myriadrf/reference-development-kit/myriadrf-1/v1/previous/VIA_OFF_PAD_v.1_r.0/PDF/MYRIAD_RF_PCB Edges.pdf

C:\Import.bin L10: MYRIAD_RF-PCB_Edges.gbr (SIG)
