myriadrf/reference-development-kit/myriadrf-1/v1/previous/VIA_OFF_PAD_v.1_r.0/PDF/MYRIAD_RF_NC Drill.pdf

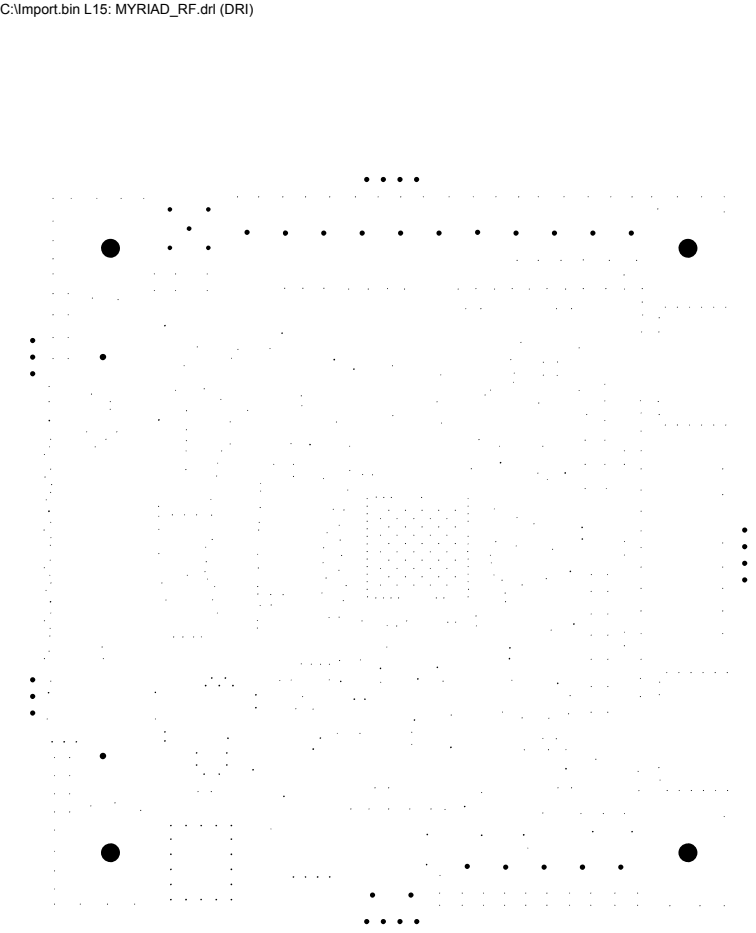
[picture p5: page 1]

C:\Import.bin L15: MYRIAD_RF.drl (DRI)
