myriadrf/reference-development-kit/myriadrf-1/v1/previous/VIA_IN_PAD_v.1_r.0/PDF/MYRIAD_RF_Drill map.pdf

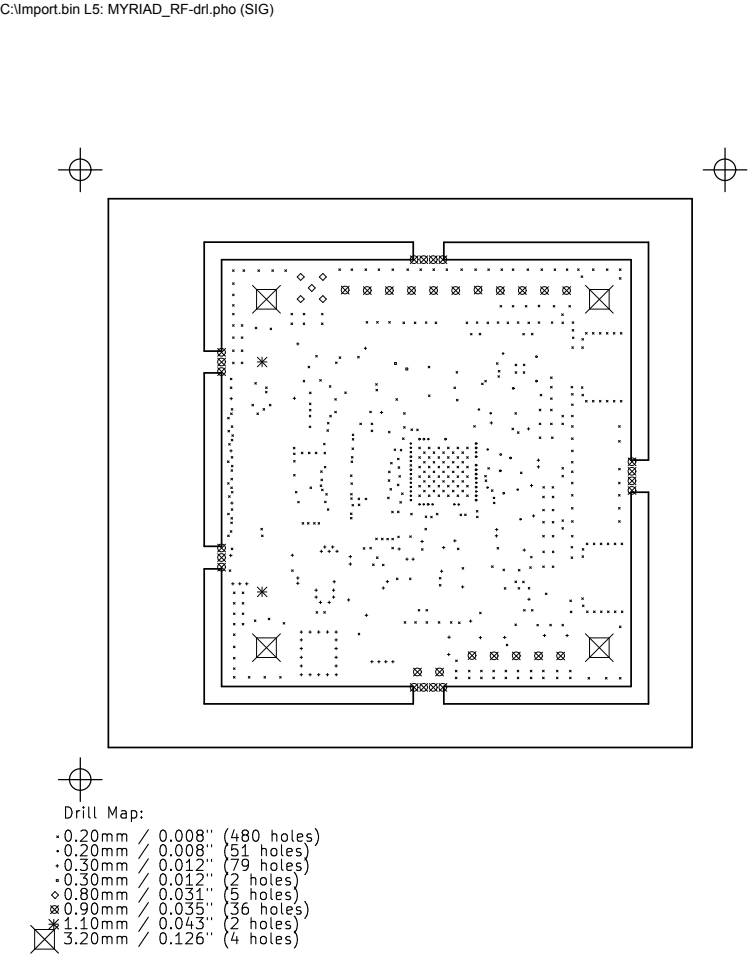
[picture p49: page 1]

C:\Import.bin L5: MYRIAD_RF-drl.pho (SIG)
