myriadrf/reference-development-kit/myriadrf-1/v1/previous/VIA_IN_PAD_v.1_r.0/PDF/MYRIAD_RF_Layouts.pdf

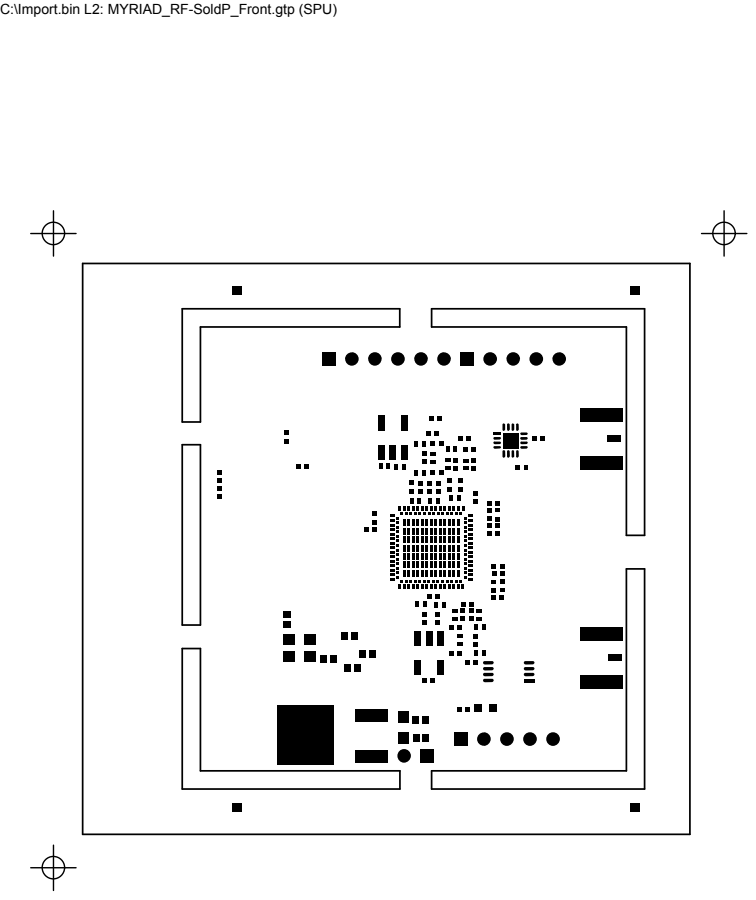
[picture p50: page 1]

C:\Import.bin L2: MYRIAD_RF-SoldP_Front.gtp (SPU)

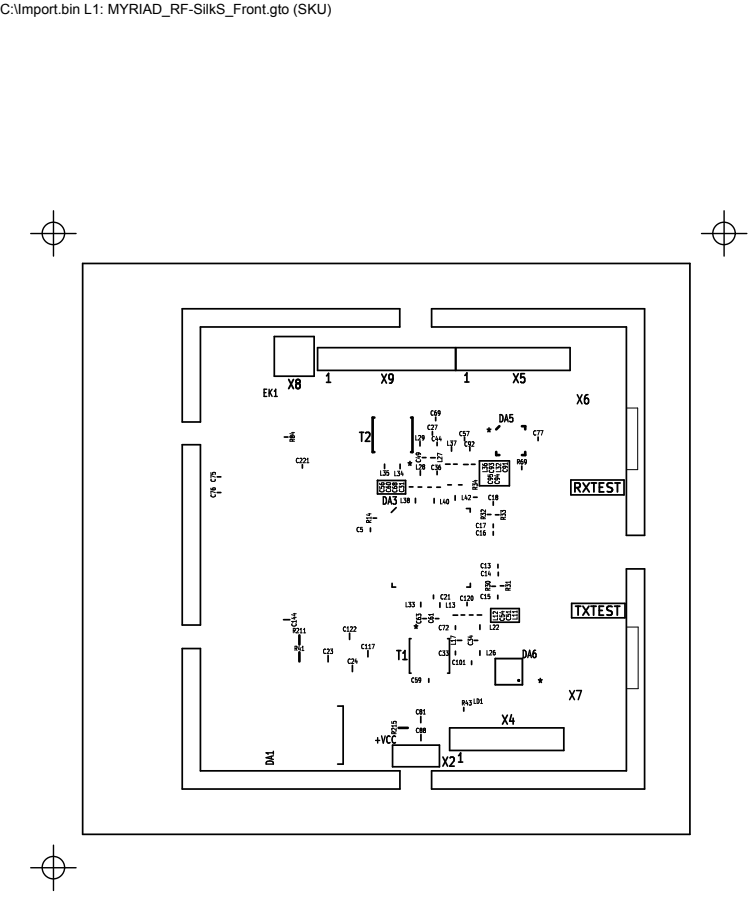
[picture p51: page 2]

C:\Import.bin L1: MYRIAD_RF-SilkS_Front.gto (SKU)

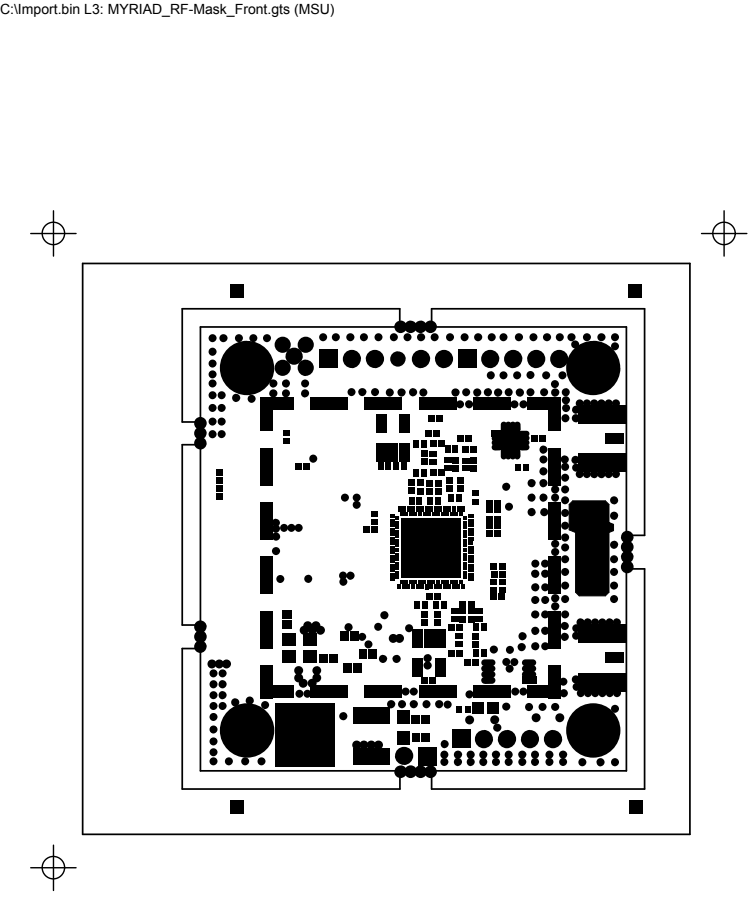
[picture p52: page 3]

C:\Import.bin L3: MYRIAD_RF-Mask_Front.gts (MSU)

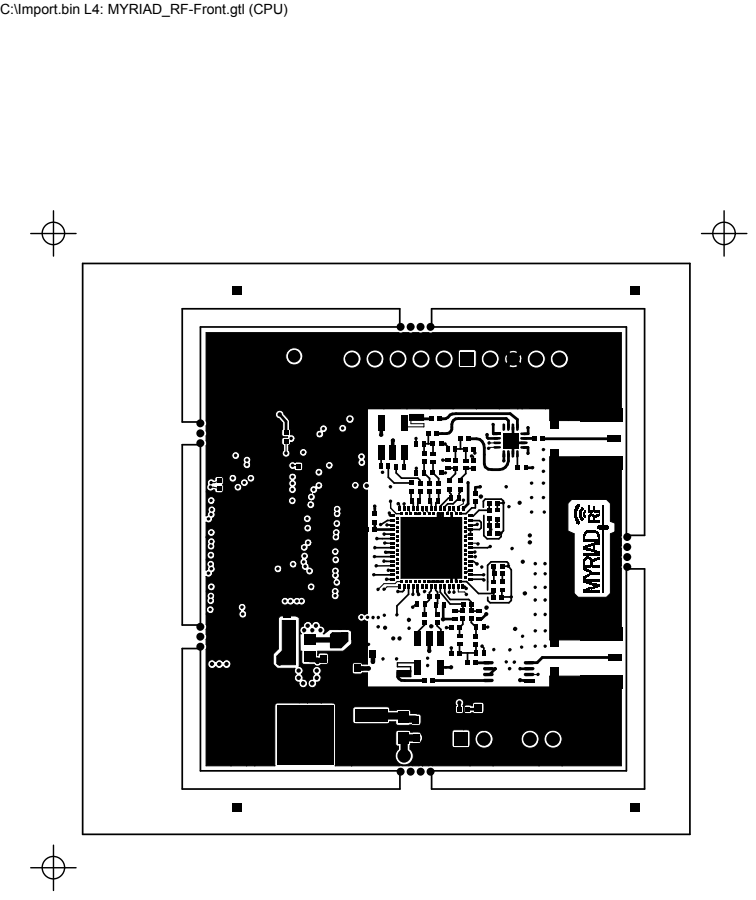
[picture p53: page 4]

C:\Import.bin L4: MYRIAD_RF-Front.gtl (CPU)

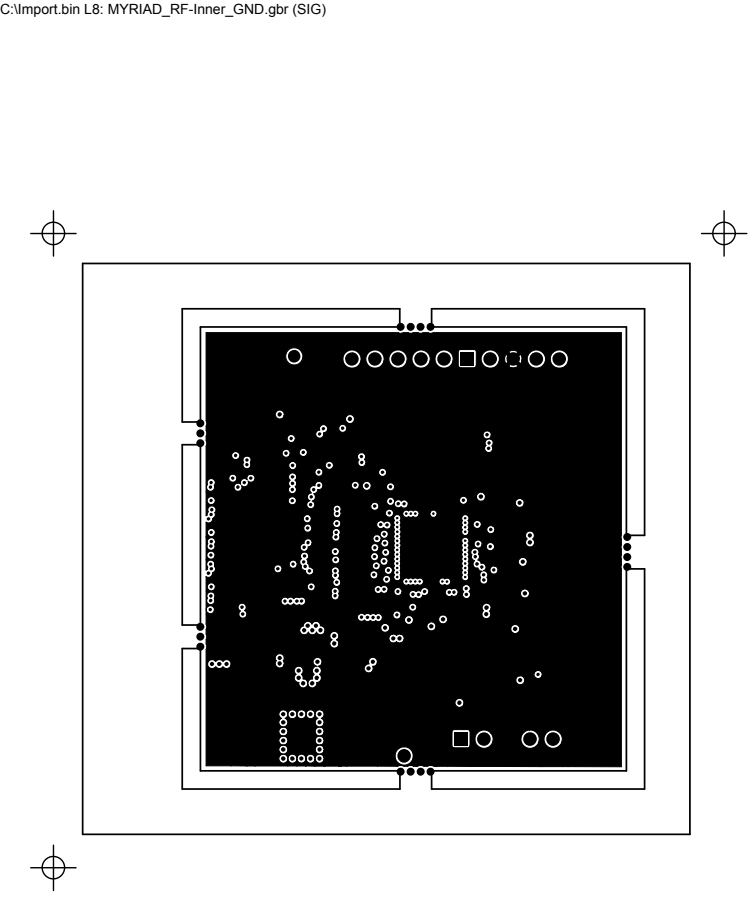
[picture p54: page 5]

C:\Import.bin L8: MYRIAD_RF-Inner_GND.gbr (SIG)

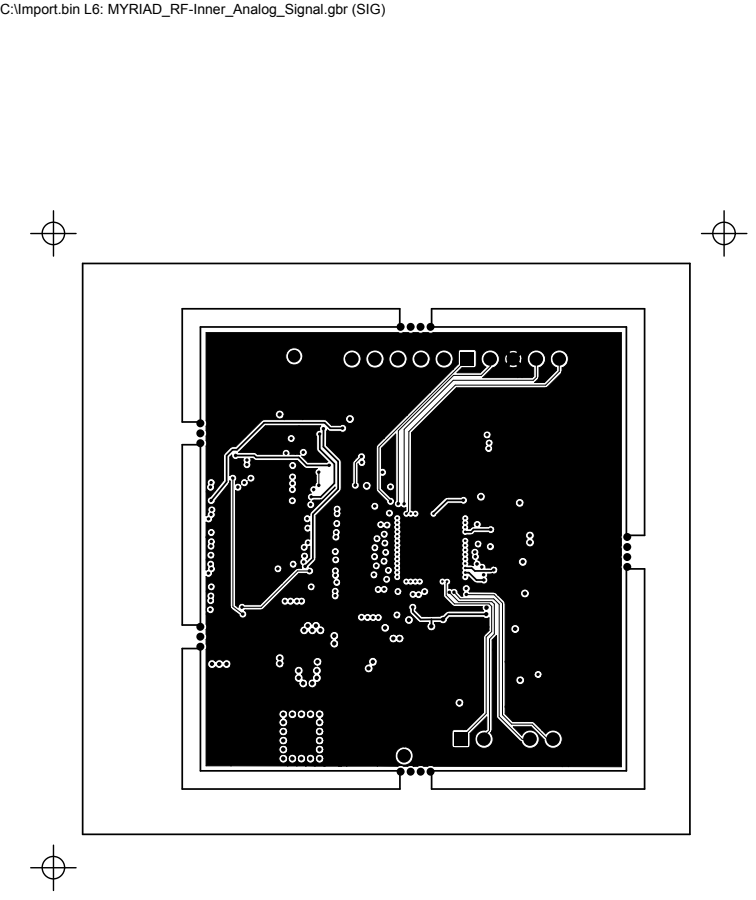
[picture p55: page 6]

C:\Import.bin L6: MYRIAD_RF-Inner_Analog_Signal.gbr (SIG)

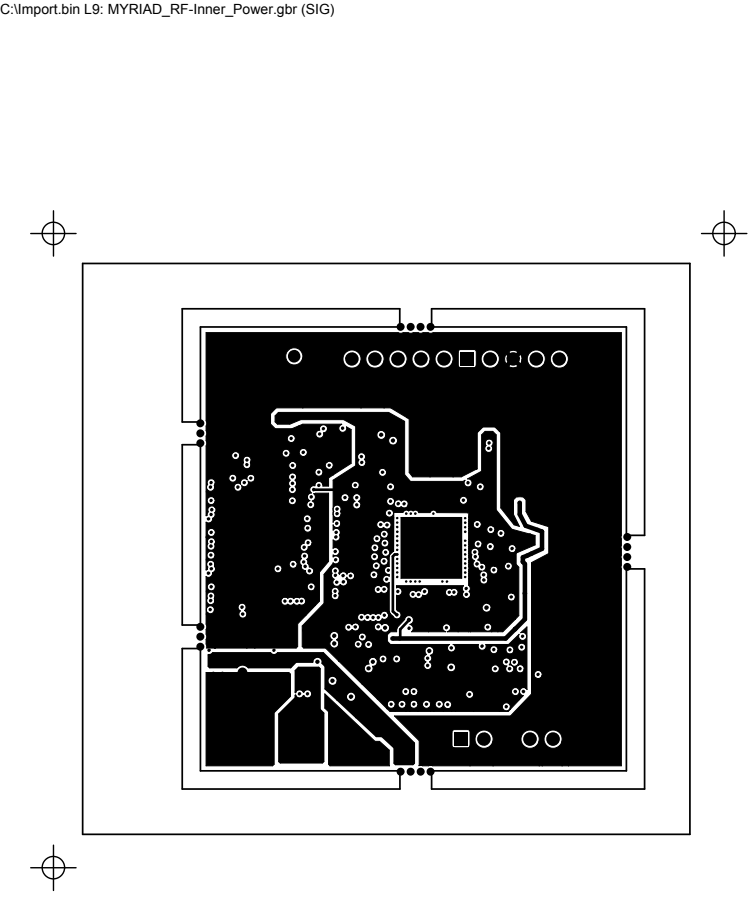
[picture p56: page 7]

C:\Import.bin L9: MYRIAD_RF-Inner_Power.gbr (SIG)

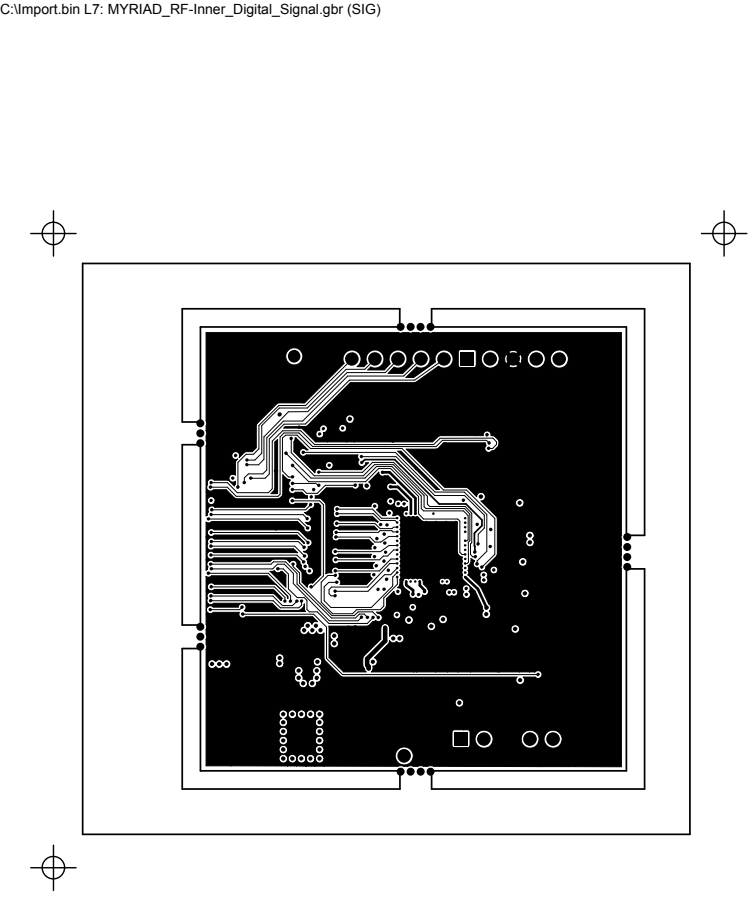
[picture p57: page 8]

C:\Import.bin L7: MYRIAD_RF-Inner_Digital_Signal.gbr (SIG)

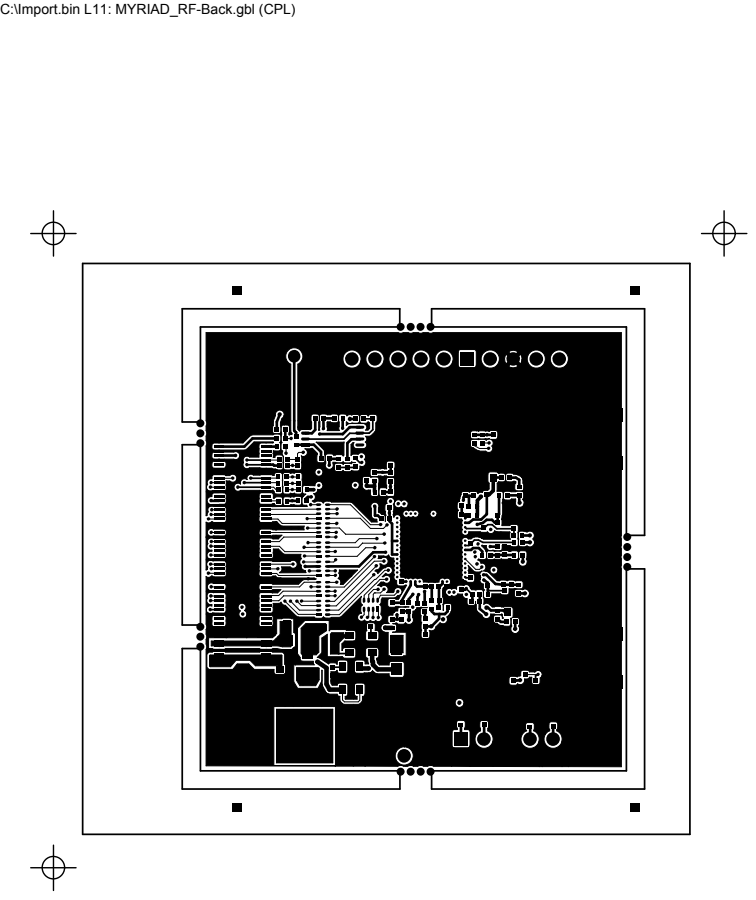
[picture p58: page 9]

C:\Import.bin L11: MYRIAD_RF-Back.gbl (CPL)

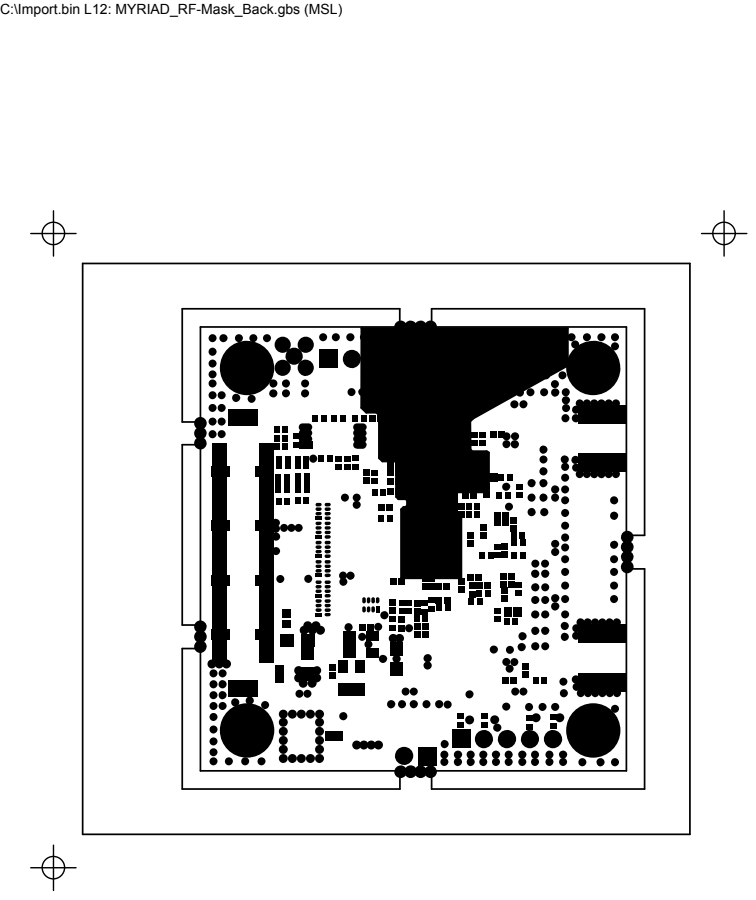
[picture p59: page 10]

C:\Import.bin L12: MYRIAD_RF-Mask_Back.gbs (MSL)

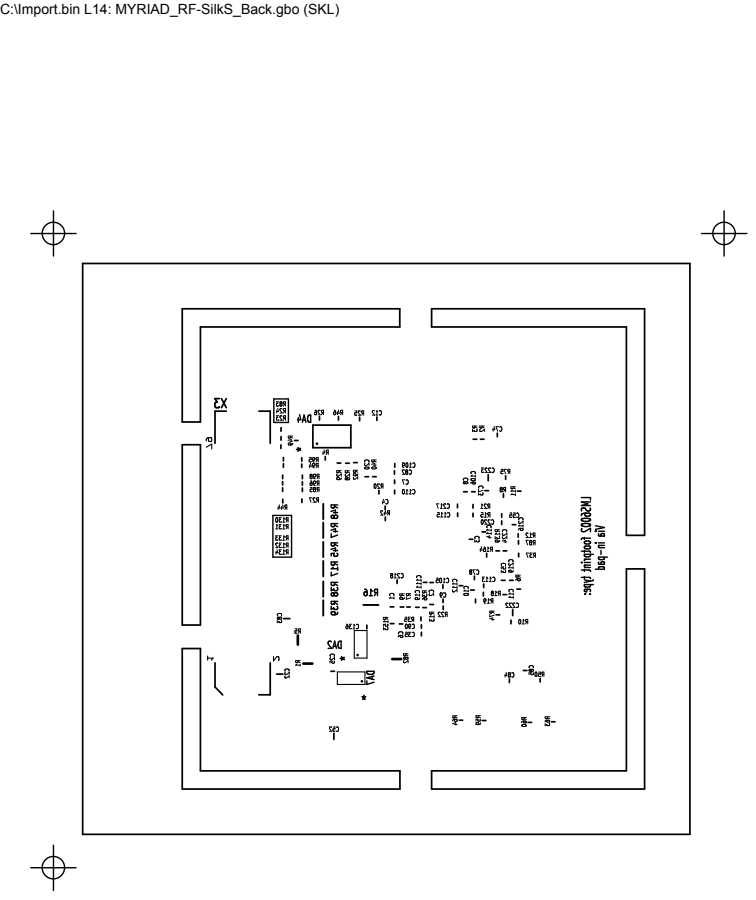
[picture p60: page 11]

C:\Import.bin L14: MYRIAD_RF-SilkS_Back.gbo (SKL)

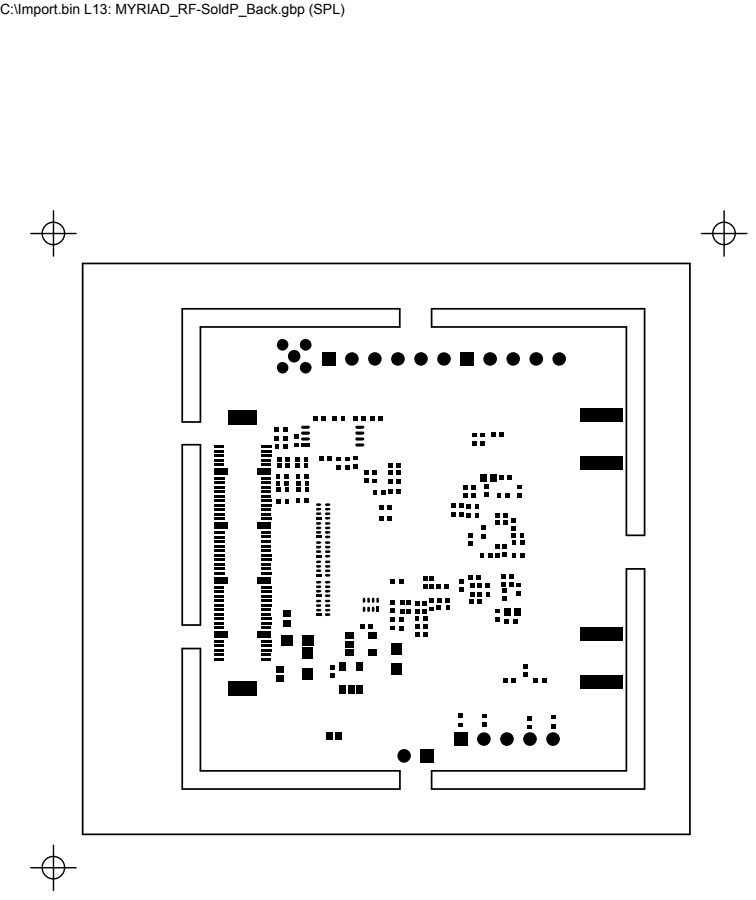
[picture p61: page 12]

C:\Import.bin L13: MYRIAD_RF-SoldP_Back.gbp (SPL)
