myriadrf/reference-development-kit/myriadrf-1/v1/VIA_IN_PAD_v.1_r.3/KiCAD Design Files/Analog Circuits.sch

## KiCad design myriadrf-1/v1/VIA_IN_PAD_v.1_r.3/KiCAD Design Files/Analog Circuits.sch (2015-12-03)

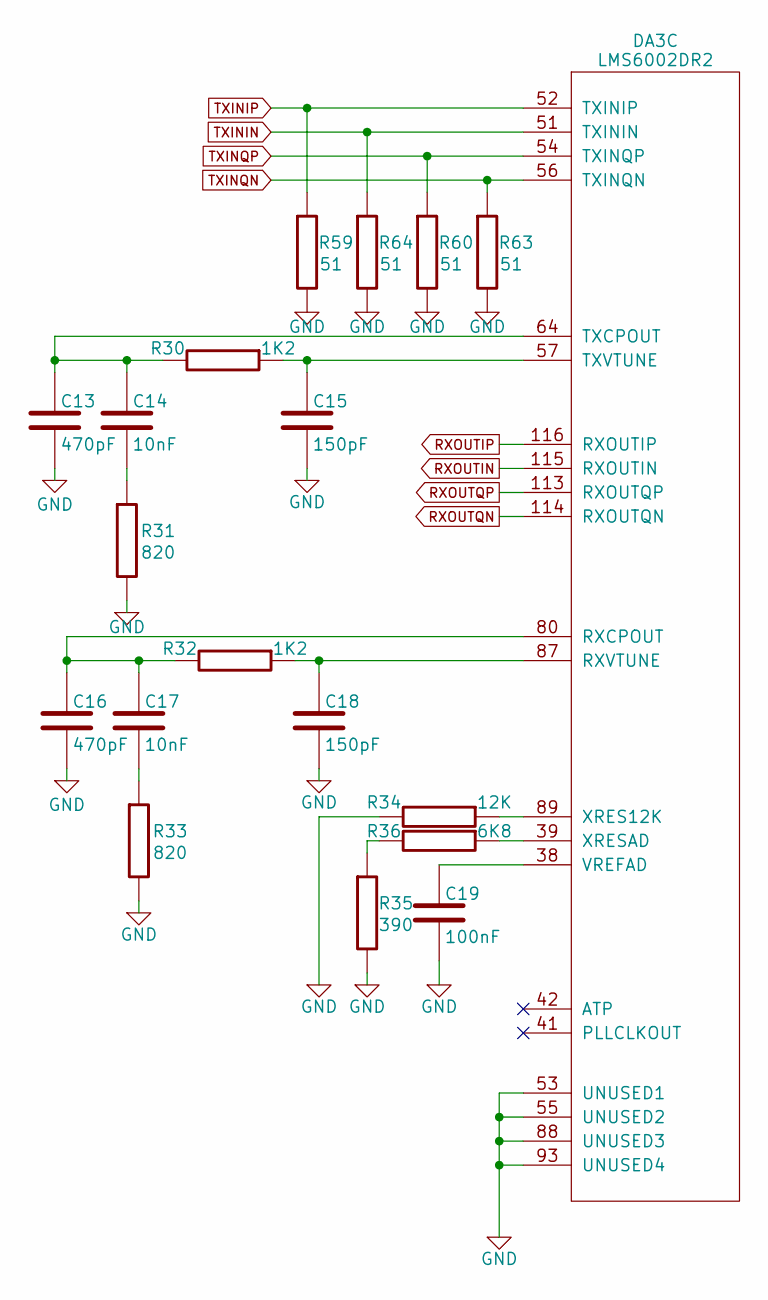
[picture p78: schematic Analog Circuits.sch]

Parts:
C13, C16: 470pF; C_SM0402; Manufacturer Part Number MCCA000132
C14, C17: 10nF; C_SM0402; Manufacturer Part Number CC0402KRX7R7BB103
C15, C18: 150pF; C_SM0402; Manufacturer Part Number MCCA000122
C19: 100nF; C_SM0402; Manufacturer Part Number C0402C104K8PACTU
DA3: LMS6002DR2; LMS6002; Manufacturer Part Number LMS6002DR2
R30, R32: 1K2; R_SM0402; Manufacturer Part Number MC 0.0625W 0402 1% 1K2
R31, R33: 820; R_SM0402; Manufacturer Part Number MC 0.0625W 0402 1% 820R
R34: 12K; R_SM0402; Manufacturer Part Number MC 0.0625W 0402 1% 12K
R35: 390; R_SM0402; Manufacturer Part Number RC0402FR-07390RL
R36: 6K8; R_SM0402; Manufacturer Part Number MC 0.0625W 0402 1% 6K8
R59, R60, R63, R64: 51; R_SM0402; Manufacturer Part Number RC0402FR-0751RL

Connections:
GND: C13.2, C15.2, C16.2, C18.2, C19.2, DA3.53 (UNUSED1), DA3.55 (UNUSED2), DA3.88 (UNUSED3), DA3.93 (UNUSED4), R31.2, R33.2, R34.2, R35.2, R59.2, R60.2, R63.2, R64.2
unnamed: C13.1, C14.1, DA3.64 (TXCPOUT), R30.2
unnamed: C14.2, R31.1
unnamed: C15.1, DA3.57 (TXVTUNE), R30.1
unnamed: C16.1, C17.1, DA3.80 (RXCPOUT), R32.2
unnamed: C17.2, R33.1
unnamed: C18.1, DA3.87 (RXVTUNE), R32.1
unnamed: C19.1, DA3.38 (VREFAD)
unnamed: DA3.39 (XRESAD), R36.1
unnamed: DA3.89 (XRES12K), R34.1
unnamed: R35.1, R36.2
RXOUTIN: DA3.115 (RXOUTIN)
RXOUTIP: DA3.116 (RXOUTIP)
RXOUTQN: DA3.114 (RXOUTQN)
RXOUTQP: DA3.113 (RXOUTQP)
TXININ: DA3.51 (TXININ), R64.1
TXINIP: DA3.52 (TXINIP), R59.1
TXINQN: DA3.56 (TXINQN), R63.1
TXINQP: DA3.54 (TXINQP), R60.1
