myriadrf/reference-development-kit/myriadrf-1/v1/VIA_IN_PAD_v.1_r.3/KiCAD Design Files/Clocks, RF FE.sch

## KiCad design myriadrf-1/v1/VIA_IN_PAD_v.1_r.3/KiCAD Design Files/Clocks, RF FE.sch (2015-12-03)

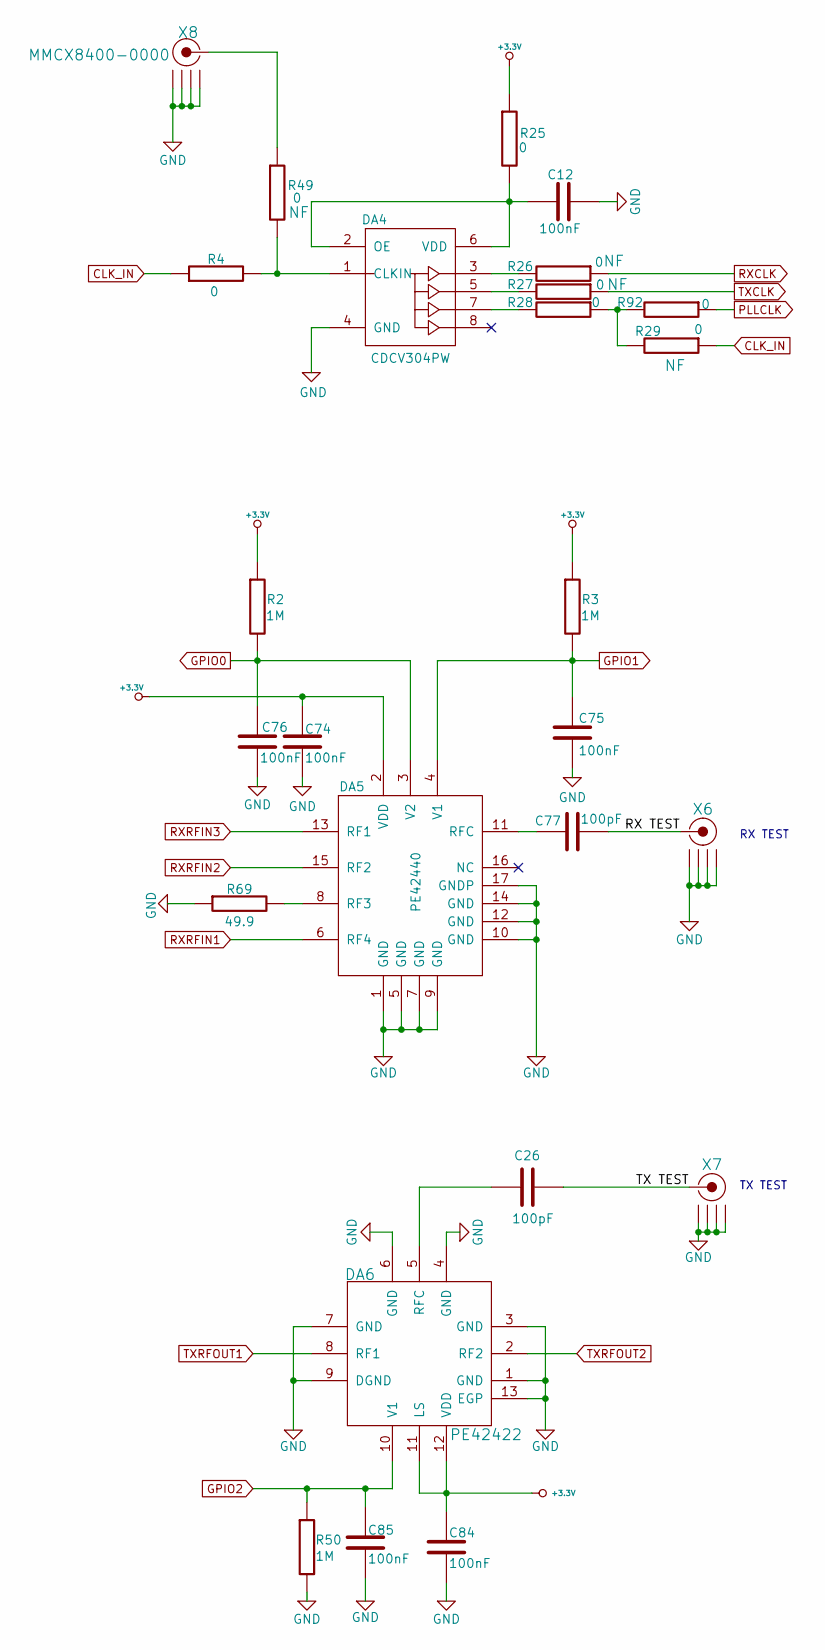
[picture p79: schematic Clocks, RF FE.sch]

Parts:
C12, C74, C75, C76, C84, C85: 100nF; C_SM0402; Manufacturer Part Number C0402C104K8PACTU
C26, C77: 100pF; C_SM0402; Manufacturer Part Number GRM1555C1H101JD01D
DA4: CDCV304PW; TSSOP-8; Manufacturer Part Number CDCV304PWR
DA5: PE42440; QFN-16; Manufacturer Part Number PE42440
DA6: PE42422; QFN12; Manufacturer Part Number PE42422MLAA-Z
R2, R3, R50: 1M; R_SM0402; Manufacturer Part Number RC0402FR-071ML
R4, R25, R26, R27, R28, R29, R49, R92: 0; R_SM0402; Manufacturer Part Number RC0402JR-070RL
R69: 49.9; R_SM0402; Manufacturer Part Number MC 0.0625W 0402 1% 49R9
X6, X7: SMA8401-0000; SMA; Manufacturer Part Number SMA8401-0000
X8: MMCX8400-0000; MMCX; Manufacturer Part Number MMCX8400-0000

Connections:
+3.3V: C74.1, C84.1, DA5.2 (VDD), DA6.11 (LS), DA6.12 (VDD), R2.1, R3.1, R25.1
CLK_IN: R4.1, R29.1
GND: C12.2, C74.2, C75.2, C76.2, C84.2, C85.2, DA4.4 (GND), DA5.1 (GND), DA5.5 (GND), DA5.7 (GND), DA5.9 (GND), DA5.10 (GND), DA5.12 (GND), DA5.14 (GND), DA5.17 (GNDP), DA6.1 (GND), DA6.3 (GND), DA6.4 (GND), DA6.6 (GND), DA6.7 (GND), DA6.9 (DGND), DA6.13 (EGP), R50.2, R69.1, X6.2 (GND1), X6.3 (GND2), X6.4 (GND3), X6.5 (GND4), X7.2 (GND1), X7.3 (GND2), X7.4 (GND3), X7.5 (GND4), X8.2 (GND1), X8.3 (GND2), X8.4 (GND3), X8.5 (GND4)
GPIO0: C76.1, DA5.3 (V2), R2.2
GPIO1: C75.1, DA5.4 (V1), R3.2
GPIO2: C85.1, DA6.10 (V1), R50.1
unnamed: C12.1, DA4.2 (OE), DA4.6 (VDD), R25.2
unnamed: C26.1, DA6.5 (RFC)
unnamed: C77.1, DA5.11 (RFC)
unnamed: DA4.1 (CLKIN), R4.2, R49.2
unnamed: DA4.3, R26.2
unnamed: DA4.5, R27.2
unnamed: DA4.7, R28.2
unnamed: DA5.8 (RF3), R69.2
unnamed: R28.1, R29.2, R92.2
unnamed: R49.1, X8.1 (RF)
PLLCLK: R92.1
RX TEST: C77.2, X6.1 (RF)
RXCLK: R26.1
RXRFIN1: DA5.6 (RF4)
RXRFIN2: DA5.15 (RF2)
RXRFIN3: DA5.13 (RF1)
TX TEST: C26.2, X7.1 (RF)
TXCLK: R27.1
TXRFOUT1: DA6.8 (RF1)
TXRFOUT2: DA6.2 (RF2)

Notes on the sheet:
TX TEST
RX TEST
