myriadrf/reference-development-kit/myriadrf-1/v1/VIA_IN_PAD_v.1_r.3/KiCAD Design Files/Connectors.sch

## KiCad design myriadrf-1/v1/VIA_IN_PAD_v.1_r.3/KiCAD Design Files/Connectors.sch (2015-12-03)

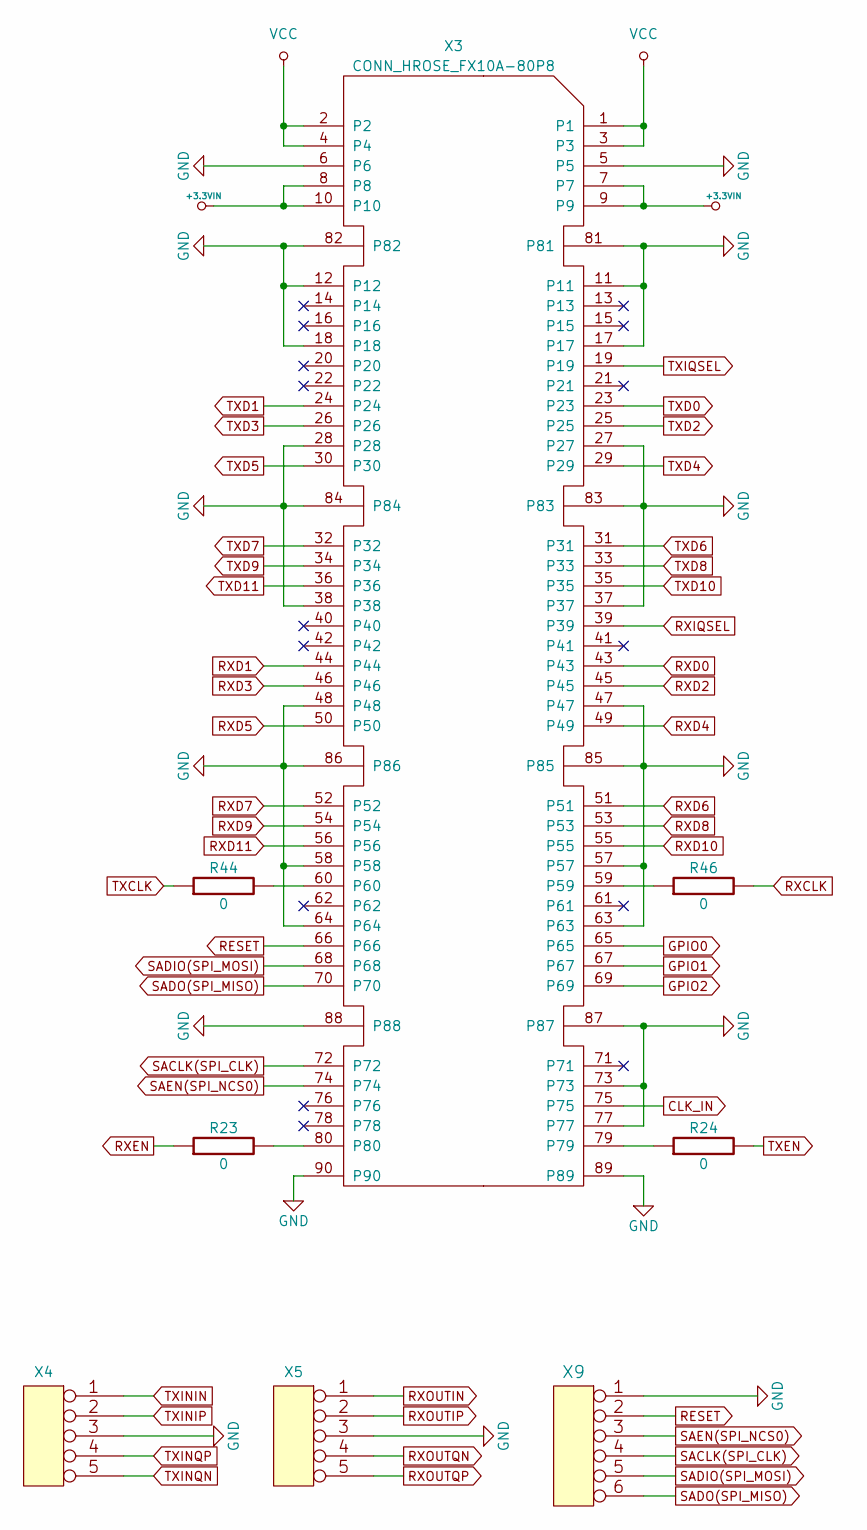
[picture p80: schematic Connectors.sch]

Parts:
R23, R24, R44, R46: 0; R_SM0402; Manufacturer Part Number RC0402JR-070RL
X3: CONN_HROSE_FX10A-80P8; FX10A-80P8; Manufacturer Part Number FX10B-80P/8-SV1(71)
X4, X5: 5-104348-3; VR_pinhead5; Manufacturer Part Number 5-104348-3
X9: CONN_6; pinhead6; Manufacturer Part Number 104345-4

Connections:
+3.3VIN: X3.7, X3.8, X3.9, X3.10
CLK_IN: X3.75
GND: X3.5, X3.6, X3.11, X3.12, X3.17, X3.18, X3.27, X3.28, X3.37, X3.38, X3.47, X3.48, X3.57, X3.58, X3.63, X3.64, X3.73, X3.77, X3.81, X3.82, X3.83, X3.84, X3.85, X3.86, X3.87, X3.88, X3.89, X3.90, X4.3, X5.3, X9.1
GPIO0: X3.65
GPIO1: X3.67
GPIO2: X3.69
unnamed: R23.2, X3.80
unnamed: R24.1, X3.79
unnamed: R44.2, X3.60
unnamed: R46.1, X3.59
RESET: X3.66, X9.2
RXCLK: R46.2
RXD0: X3.43
RXD1: X3.44
RXD2: X3.45
RXD3: X3.46
RXD4: X3.49
RXD5: X3.50
RXD6: X3.51
RXD7: X3.52
RXD8: X3.53
RXD9: X3.54
RXD10: X3.55
RXD11: X3.56
RXEN: R23.1
RXIQSEL: X3.39
RXOUTIN: X5.1
RXOUTIP: X5.2
RXOUTQN: X5.4
RXOUTQP: X5.5
SACLK(SPI_CLK): X3.72, X9.4
SADIO(SPI_MOSI): X3.68, X9.5
SADO(SPI_MISO): X3.70, X9.6
SAEN(SPI_NCS0): X3.74, X9.3
TXCLK: R44.1
TXD0: X3.23
TXD1: X3.24
TXD2: X3.25
TXD3: X3.26
TXD4: X3.29
TXD5: X3.30
TXD6: X3.31
TXD7: X3.32
TXD8: X3.33
TXD9: X3.34
TXD10: X3.35
TXD11: X3.36
TXEN: R24.2
TXININ: X4.1
TXINIP: X4.2
TXINQN: X4.5
TXINQP: X4.4
TXIQSEL: X3.19
VCC: X3.1, X3.2, X3.3, X3.4
