myriadrf/reference-development-kit/myriadrf-1/v1/VIA_IN_PAD_v.1_r.3/KiCAD Design Files/Power Supply.sch

## KiCad design myriadrf-1/v1/VIA_IN_PAD_v.1_r.3/KiCAD Design Files/Power Supply.sch (2015-12-03)

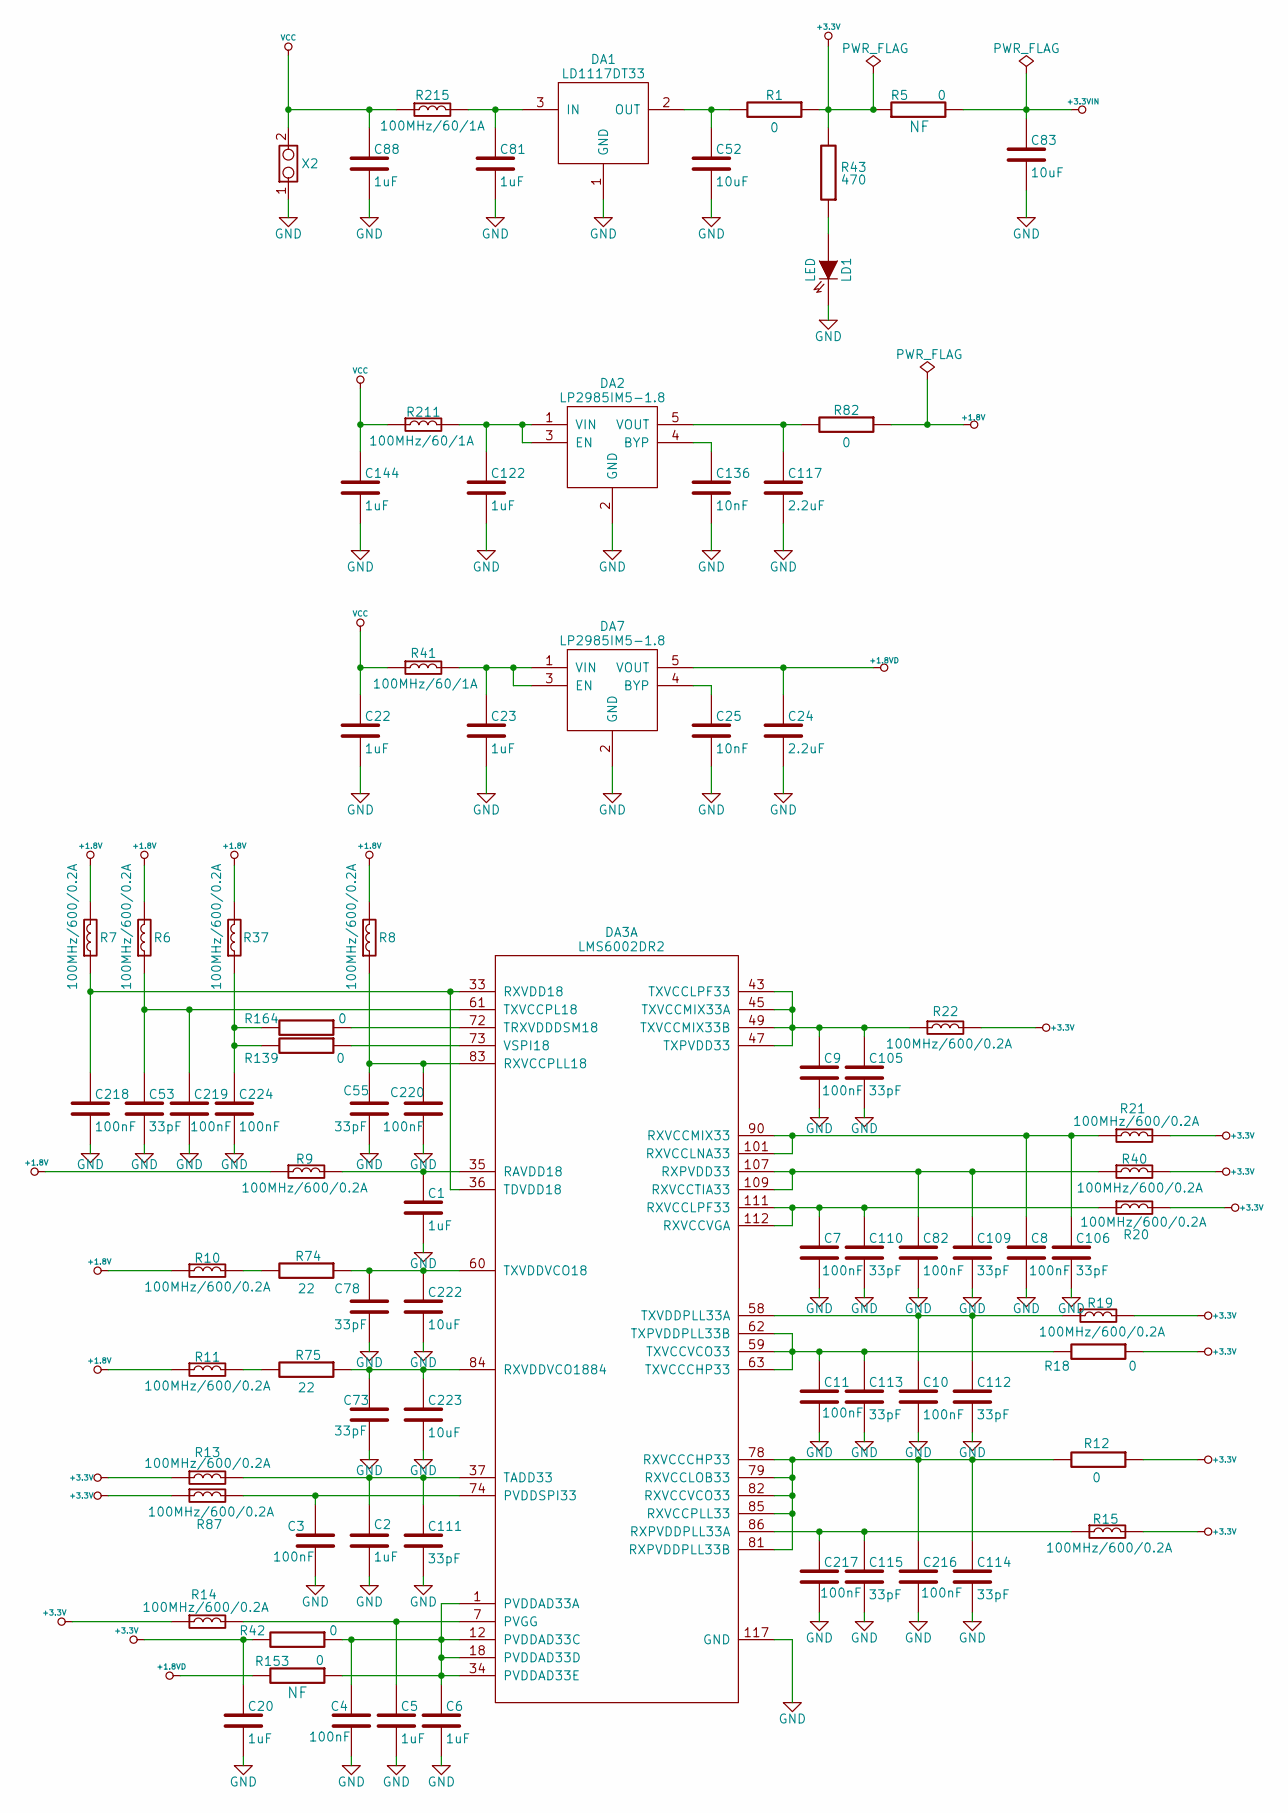
[picture p82: schematic Power Supply.sch]

Parts:
C1, C2, C5, C6, C20: 1uF; C_SM0402; Manufacturer Part Number MCCA000506
C3, C4, C7, C8, C9, C10, C11, C82, C216, C217, C218, C219, C220, C224: 100nF; C_SM0402; Manufacturer Part Number C0402C104K8PACTU
C22, C23, C81, C88, C122, C144: 1uF; C_SM0603; Manufacturer Part Number CC0603KRX5R6BB105
C24, C117: 2.2uF; C_SM0603; Manufacturer Part Number GRM188R61A225KE34D
C25, C136: 10nF; C_SM0402; Manufacturer Part Number CC0402KRX7R7BB103
C52, C83, C222, C223: 10uF; C_S0603; Manufacturer Part Number LMK107BJ106MALTD
C53, C55, C73, C78, C105, C106, C109, C110, C111, C112, C113, C114, C115: 33pF; C_SM0402; Manufacturer Part Number MCCA000902
DA1: LD1117DT33; DPAK2; Manufacturer Part Number LD1117DT33
DA2, DA7: LP2985IM5-1.8; SOT23-5; Manufacturer Part Number LP2985IM5-1.8/NOPB
DA3: LMS6002DR2; DQFN-120; Manufacturer Part Number LMS6002DR2
LD1: LED; LD0603; Manufacturer Part Number LGQ971
R1, R5, R82: 0; R_SM0805; Manufacturer Part Number RC0805JR-070RL
R6, R7, R8, R9, R10, R11, R13, R14, R15, R19, R20, R21, R22, R37, R40, R87: 100MHz/600/0.2A; R_SM0402; Manufacturer Part Number 7427927161
R12, R18, R42, R139, R153, R164: 0; R_SM0402; Manufacturer Part Number RC0402JR-070RL
R41, R211, R215: 100MHz/60/1A; R_SM0805; Manufacturer Part Number MMZ2012Y600B
R43: 470; R_SM0402; Manufacturer Part Number RC0402FR-07470RL
R74, R75: 22; R_SM0402; Manufacturer Part Number RC0402FR-0722RL
X2: 5-146285-2; pinhead2; Manufacturer Part Number 5-146285-2

Connections:
+1.8V: R6.2, R7.2, R8.2, R9.1, R10.1, R11.1, R37.2, R82.1
+1.8VD: C24.1, DA7.5 (VOUT), R153.2
+3.3V: C20.1, R1.1, R5.1, R12.1, R13.1, R14.1, R15.2, R18.1, R19.2, R20.2, R21.2, R22.2, R40.2, R42.2, R43.2, R87.1
+3.3VIN: C83.1, R5.2
GND: C1.2, C2.2, C3.2, C4.2, C5.2, C6.2, C7.2, C8.2, C9.2, C10.2, C11.2, C20.2, C22.2, C23.2, C24.2, C25.2, C52.2, C53.2, C55.2, C73.2, C78.2, C81.2, C82.2, C83.2, C88.2, C105.2, C106.2, C109.2, C110.2, C111.2, C112.2, C113.2, C114.2, C115.2, C117.2, C122.2, C136.2, C144.2, C216.2, C217.2, C218.2, C219.2, C220.2, C222.2, C223.2, C224.2, DA1.1 (GND), DA2.2 (GND), DA3.117 (GND), DA7.2 (GND), LD1.2 (K), X2.1
unnamed: C1.1, DA3.35 (RAVDD18), R9.2
unnamed: C3.1, DA3.74 (PVDDSPI33), R87.2
unnamed: C4.1, C6.1, DA3.1 (PVDDAD33A), DA3.12 (PVDDAD33C), DA3.18 (PVDDAD33D), DA3.34 (PVDDAD33E), R42.1, R153.1
unnamed: C5.1, DA3.7 (PVGG), R14.2
unnamed: C10.1, C112.1, DA3.58 (TXVDDPLL33A), R19.1
unnamed: C11.1, C113.1, DA3.59 (TXVCCVCO33), DA3.62 (TXPVDDPLL33B), DA3.63 (TXVCCCHP33), R18.2
unnamed: C23.1, DA7.1 (VIN), DA7.3 (EN), R41.2
unnamed: C25.1, DA7.4 (BYP)
unnamed: C52.1, DA1.2 (OUT), R1.2
unnamed: C81.1, DA1.3 (IN), R215.2
unnamed: C9.1, C105.1, DA3.43 (TXVCCLPF33), DA3.45 (TXVCCMIX33A), DA3.47 (TXPVDD33), DA3.49 (TXVCCMIX33B), R22.1
unnamed: C8.1, C106.1, DA3.90 (RXVCCMIX33), DA3.101 (RXVCCLNA33), R21.1
unnamed: C82.1, C109.1, DA3.107 (RXPVDD33), DA3.109 (RXVCCTIA33), R40.1
unnamed: C7.1, C110.1, DA3.111 (RXVCCLPF33), DA3.112 (RXVCCVGA), R20.1
unnamed: C2.1, C111.1, DA3.37 (TADD33), R13.2
unnamed: C114.1, C216.1, DA3.78 (RXVCCCHP33), DA3.79 (RXVCCLOB33), DA3.81 (RXPVDDPLL33B), DA3.82 (RXVCCVCO33), DA3.85 (RXVCCPLL33), R12.2
unnamed: C115.1, C217.1, DA3.86 (RXPVDDPLL33A), R15.1
unnamed: C117.1, DA2.5 (VOUT), R82.2
unnamed: C122.1, DA2.1 (VIN), DA2.3 (EN), R211.2
unnamed: C136.1, DA2.4 (BYP)
unnamed: C218.1, DA3.33 (RXVDD18), DA3.36 (TDVDD18), R7.1
unnamed: C53.1, C219.1, DA3.61 (TXVCCPL18), R6.1
unnamed: C55.1, C220.1, DA3.83 (RXVCCPLL18), R8.1
unnamed: C78.1, C222.1, DA3.60 (TXVDDVCO18), R74.1
unnamed: C73.1, C223.1, DA3.84 (RXVDDVCO1884), R75.1
unnamed: C224.1, R37.1, R139.2, R164.2
unnamed: DA3.72 (TRXVDDDSM18), R164.1
unnamed: DA3.73 (VSPI18), R139.1
unnamed: LD1.1 (A), R43.1
unnamed: R10.2, R74.2
unnamed: R11.2, R75.2
VCC: C22.1, C88.1, C144.1, R41.1, R211.1, R215.1, X2.2
