myriadrf/reference-development-kit/myriadrf-1/v1/VIA_IN_PAD_v.1_r.3/KiCAD Design Files/RF Circuits.sch

## KiCad design myriadrf-1/v1/VIA_IN_PAD_v.1_r.3/KiCAD Design Files/RF Circuits.sch (2015-12-03)

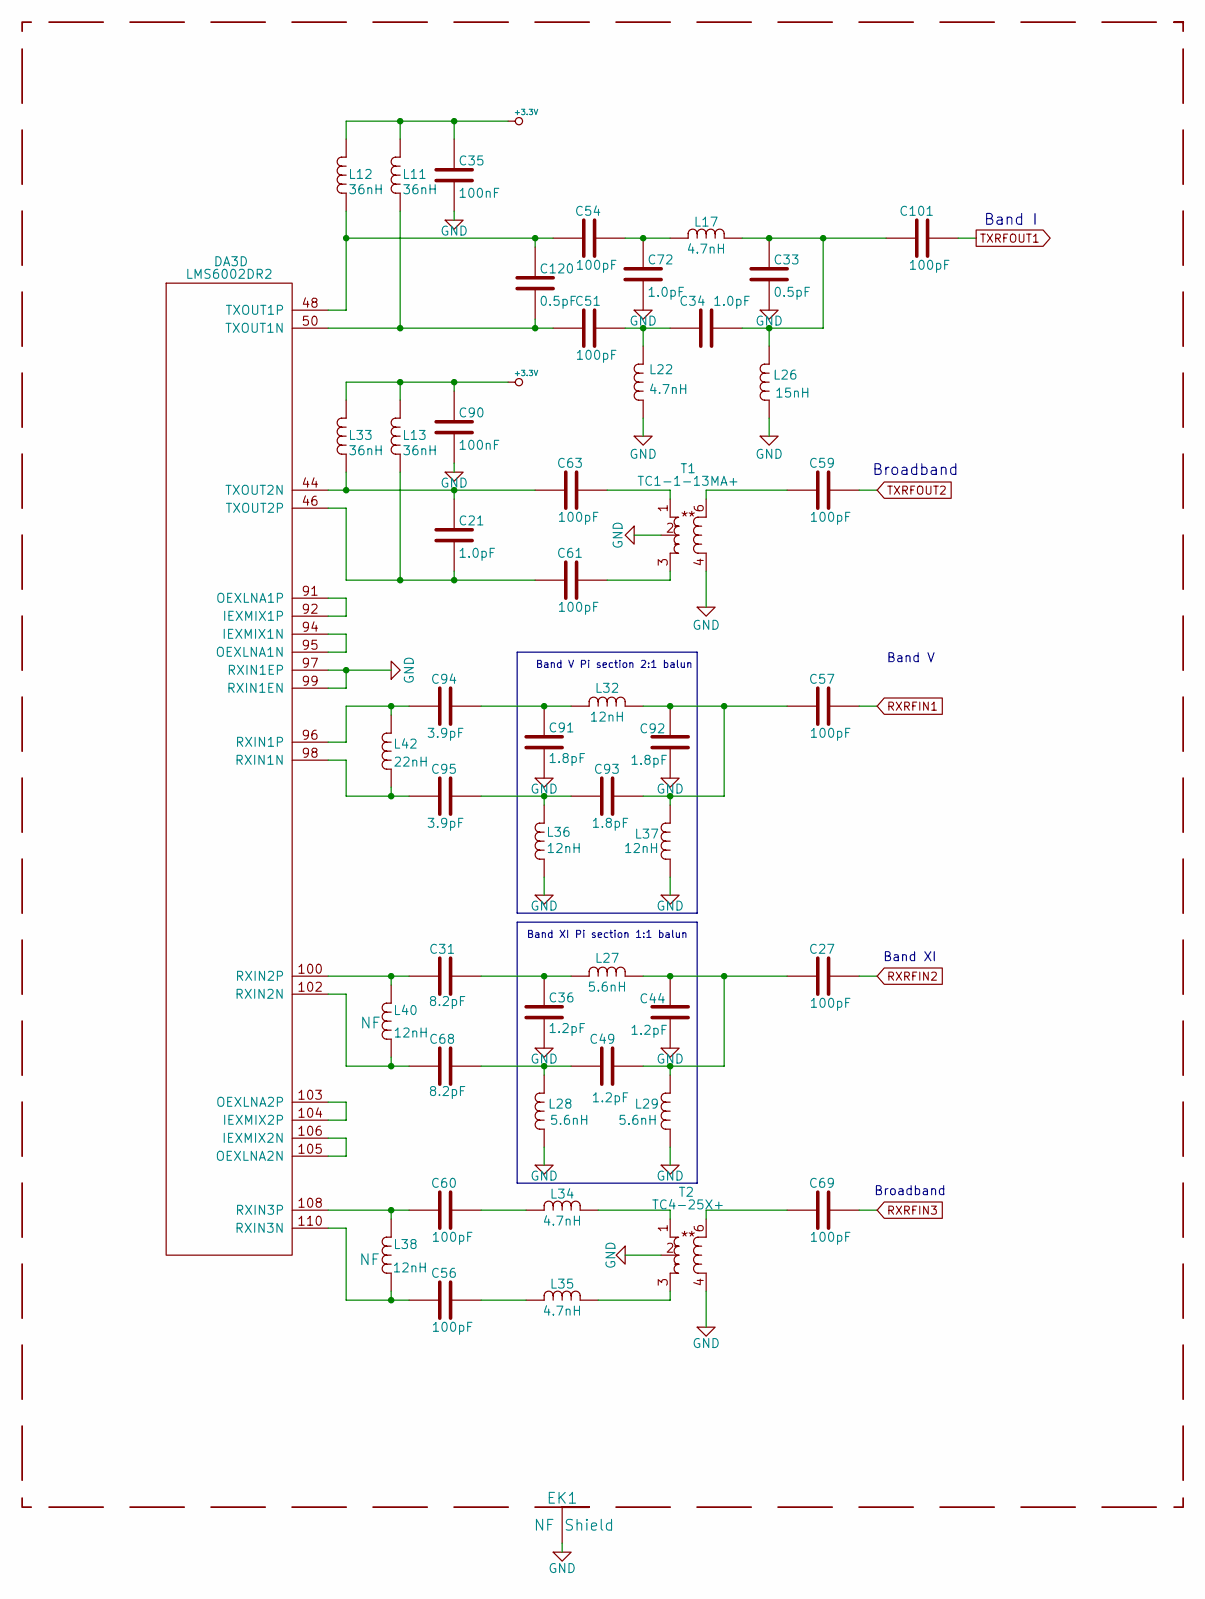
[picture p83: schematic RF Circuits.sch]

Parts:
C21, C34, C72: 1.0pF; C_SM0402; Manufacturer Part Number GJM1555C1H1R0BB01D
C27, C51, C54, C56, C57, C59, C60, C61, C63, C69, C101: 100pF; C_SM0402; Manufacturer Part Number GRM1555C1H101JD01D
C31, C68: 8.2pF; C_SM0402; Manufacturer Part Number C0402C829C5GACTU
C33, C120: 0.5pF; C_SM0402; Manufacturer Part Number CC0402CRNPO9BNR50
C35, C90: 100nF; C_SM0402; Manufacturer Part Number C0402C104K8PACTU
C36, C44, C49: 1.2pF; C_SM0402; Manufacturer Part Number CBR04C129B1GAC
C91, C92, C93: 1.8pF; C_SM0402; Manufacturer Part Number CBR04C189B1GAC
C94, C95: 3.9pF; C_SM0402; Manufacturer Part Number CBR04C399B1GAC
DA3: LMS6002DR2; LMS6002; Manufacturer Part Number LMS6002DR2
EK1: Shield; EK; Manufacturer Part Number BMI-S-204-F
L11, L12, L13, L33: 36nH; L_SM0402; Manufacturer Part Number 0402CS-36NX_LU
L17, L22, L34, L35: 4.7nH; L_SM0402; Manufacturer Part Number 0402HP-4N7X_LU
L26: 15nH; L_SM0402; Manufacturer Part Number 0402HP-15NX_LU
L27, L28, L29: 5.6nH; L_SM0402; Manufacturer Part Number 0402HP-5N6XJLU
L32, L36, L37, L38, L40: 12nH; L_SM0402; Manufacturer Part Number 0402HP-12NX_LU
L42: 22nH; L_SM0402; Manufacturer Part Number 0402HP-22NX_LU
T1: TC1-1-13MA+; Manufacturer Part Number TC1-1-13MA+
T2: TC4-25X+; TC1-1-13MA+; Manufacturer Part Number TC4-25X+

Connections:
+3.3V: C35.1, C90.1, L11.1, L12.1, L13.1, L33.1
GND: C33.2, C35.2, C36.2, C44.2, C72.2, C90.2, C91.2, C92.2, DA3.97 (RXIN1EP), DA3.99 (RXIN1EN), EK1.1, L22.2, L26.2, L28.2, L29.2, L36.2, L37.2, T1.2, T1.4, T2.2, T2.4
unnamed: C21.1, C63.1, DA3.44 (TXOUT2N), L33.2
unnamed: C21.2, C61.1, DA3.46 (TXOUT2P), L13.2
unnamed: C27.1, C44.1, C49.2, L27.1, L29.1
unnamed: C31.1, DA3.100 (RXIN2P), L40.1
unnamed: C31.2, C36.1, L27.2
unnamed: C34.1, C51.2, L22.1
unnamed: C49.1, C68.2, L28.1
unnamed: C54.2, C72.1, L17.2
unnamed: C56.1, DA3.110 (RXIN3N), L38.2
unnamed: C56.2, L35.2
unnamed: C57.1, C92.1, C93.2, L32.1, L37.1
unnamed: C59.1, T1.6
unnamed: C60.1, DA3.108 (RXIN3P), L38.1
unnamed: C60.2, L34.2
unnamed: C61.2, T1.3
unnamed: C63.2, T1.1
unnamed: C68.1, DA3.102 (RXIN2N), L40.2
unnamed: C69.1, T2.6
unnamed: C91.1, C94.2, L32.2
unnamed: C93.1, C95.2, L36.1
unnamed: C94.1, DA3.96 (RXIN1P), L42.1
unnamed: C95.1, DA3.98 (RXIN1N), L42.2
unnamed: C33.1, C34.2, C101.1, L17.1, L26.1
unnamed: C54.1, C120.1, DA3.48 (TXOUT1P), L12.2
unnamed: C51.1, C120.2, DA3.50 (TXOUT1N), L11.2
unnamed: DA3.91 (OEXLNA1P), DA3.92 (IEXMIX1P)
unnamed: DA3.94 (IEXMIX1N), DA3.95 (OEXLNA1N)
unnamed: DA3.103 (OEXLNA2P), DA3.104 (IEXMIX2P)
unnamed: DA3.105 (OEXLNA2N), DA3.106 (IEXMIX2N)
unnamed: L34.1, T2.1
unnamed: L35.1, T2.3
RXRFIN1: C57.2
RXRFIN2: C27.2
RXRFIN3: C69.2
TXRFOUT1: C101.2
TXRFOUT2: C59.2

Notes on the sheet:
Band XI Pi section 1:1 balun
Band V Pi section 2:1 balun
Band I
Broadband
Band V
Band XI
Broadband
